Incomprehensible/Flashlight_weapon/Renders&Graphics/21_NAD_flashlight_2_EDIT_1.png

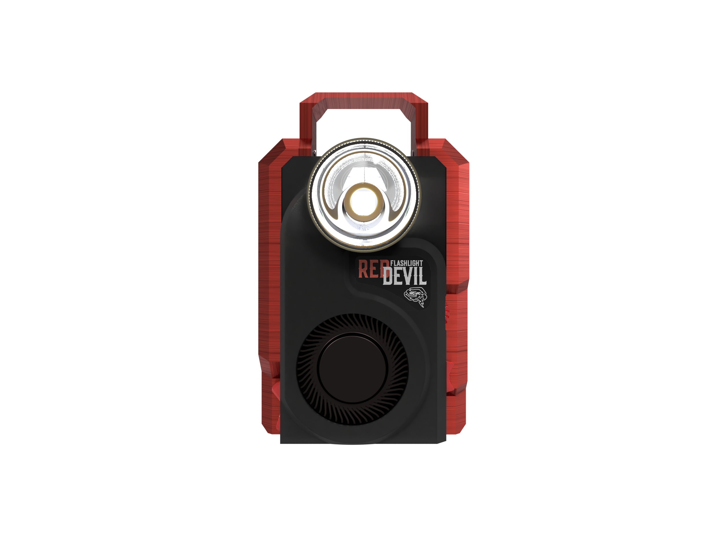
Renders&Graphics/21_NAD_flashlight_2_EDIT_1.png
