Incomprehensible/Flashlight_weapon/Renders&Graphics/21_NAD_flashlight_front_13.png

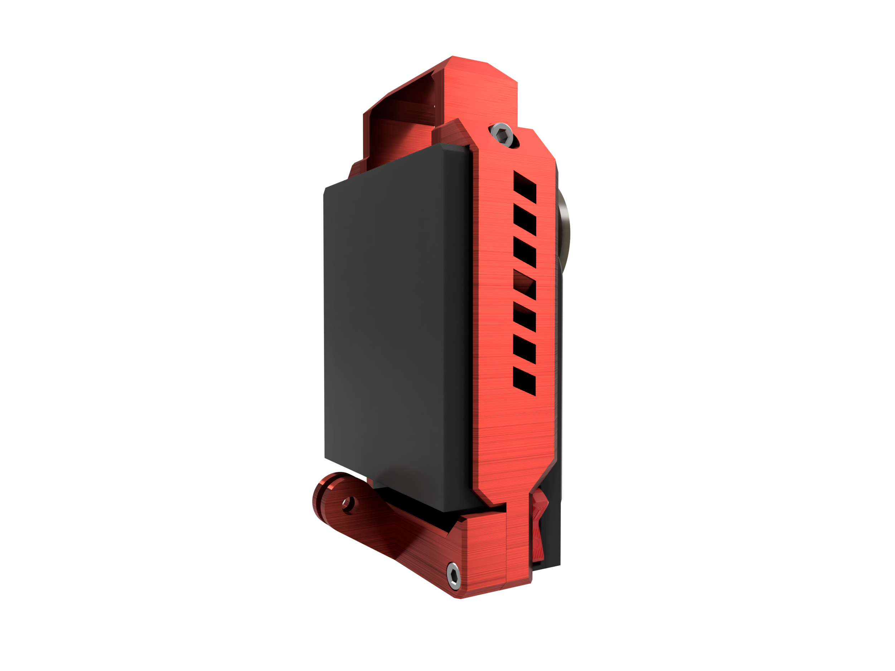
Renders&Graphics/21_NAD_flashlight_front_13.png
