Incomprehensible/Flashlight_weapon/Renders&Graphics/21_NAD_flashlight_front_18.PNG

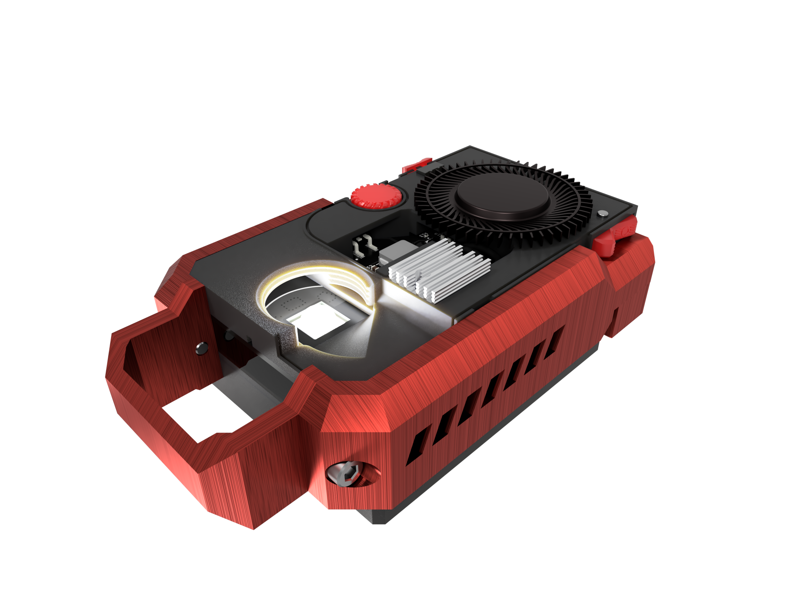
Renders&Graphics/21_NAD_flashlight_front_18.PNG
