Incomprehensible/Flashlight_weapon/KiCad/3D/XT30PW-F.stp

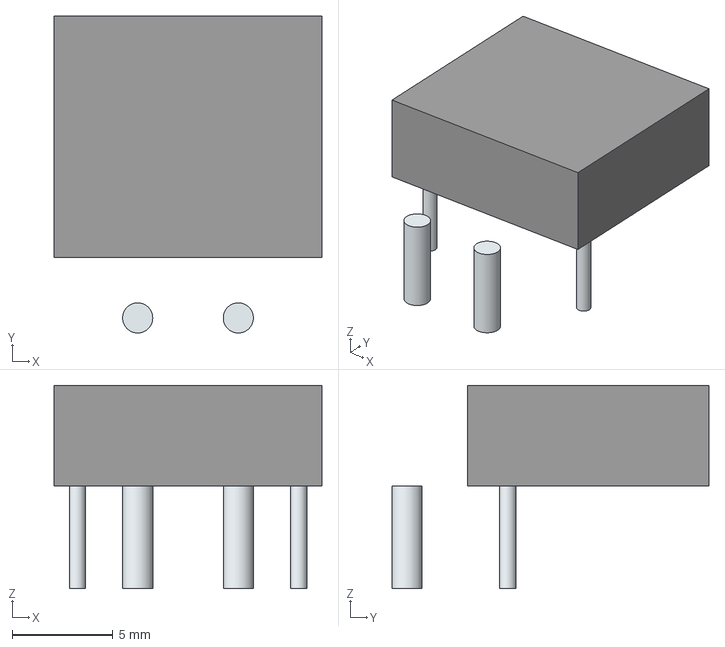
[picture p26: CAD file, 2021-12-03]
KiCad/3D/XT30PW-F.stp
13.3 x 15.7 x 10.1 mm
Leads x 4
