Incomprehensible/Flashlight_weapon/3D_models/Files_for_prototype/Selector_cap_ANY.3mf

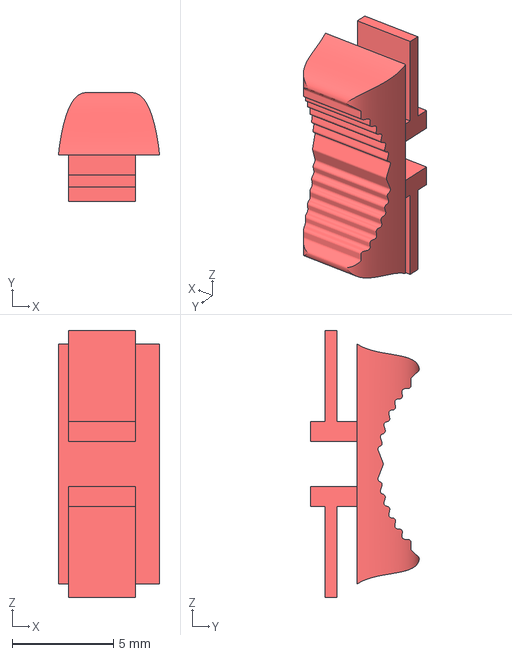
[picture p27: CAD file, 2022-10-16]
3D_models/Files_for_prototype/Selector_cap_ANY.3mf
5.00 x 5.37 x 13.2 mm
