Incomprehensible/Flashlight_weapon/KiCad/3D/IHLP4040DZER2R2M01.stp

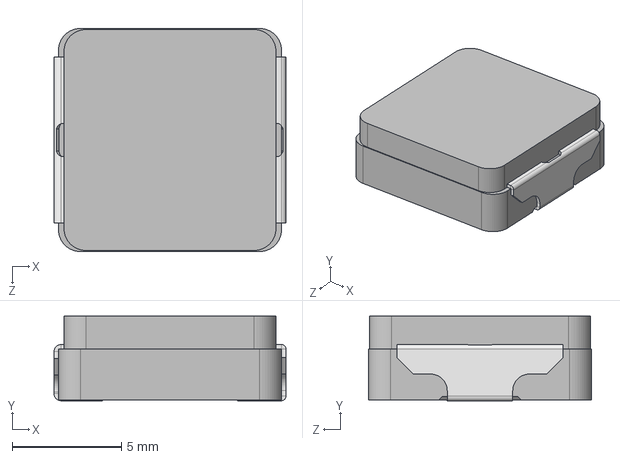
[picture p28: CAD file, 2021-12-03]
KiCad/3D/IHLP4040DZER2R2M01.stp
10.6 x 3.87 x 10.2 mm
