Incomprehensible/Flashlight_weapon/KiCad/3D/VZ067TL1B502.stp

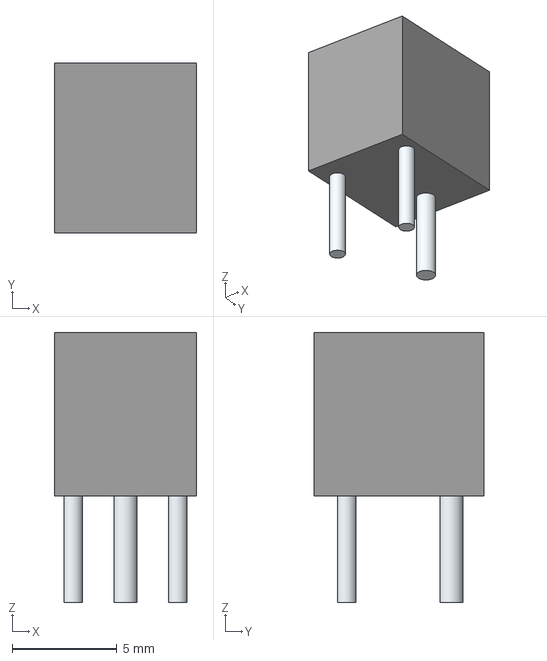
[picture p29: CAD file, 2021-12-03]
KiCad/3D/VZ067TL1B502.stp
6.80 x 8.10 x 12.9 mm
Leads x 3
