Incomprehensible/Flashlight_weapon/3D_models/Files_for_production/2LVL_battery_NYLON_PA12.step

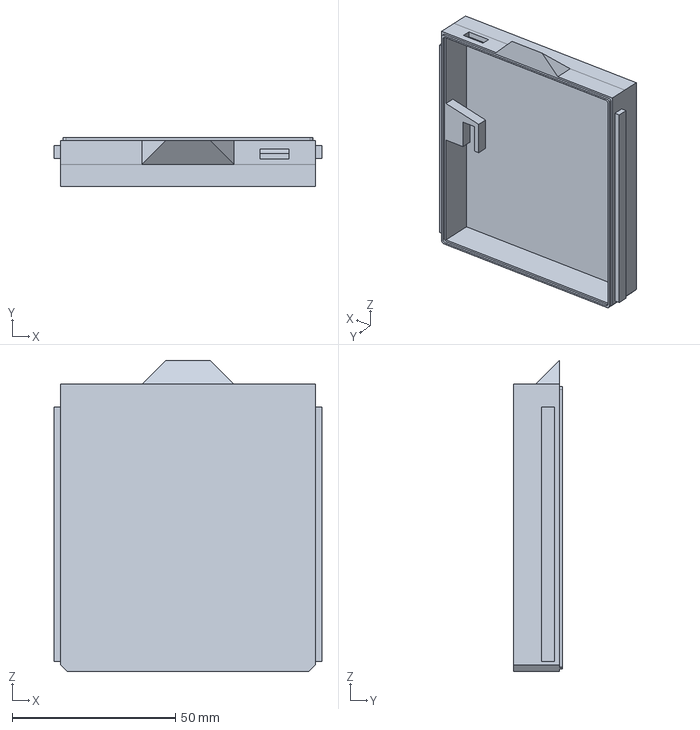
[picture p30: CAD file, 2022-10-16]
3D_models/Files_for_production/2LVL_battery_NYLON_PA12.step
82.0 x 14.9 x 95.2 mm
