Incomprehensible/Flashlight_weapon/KiCad/3D/10TPE47MAZB.step

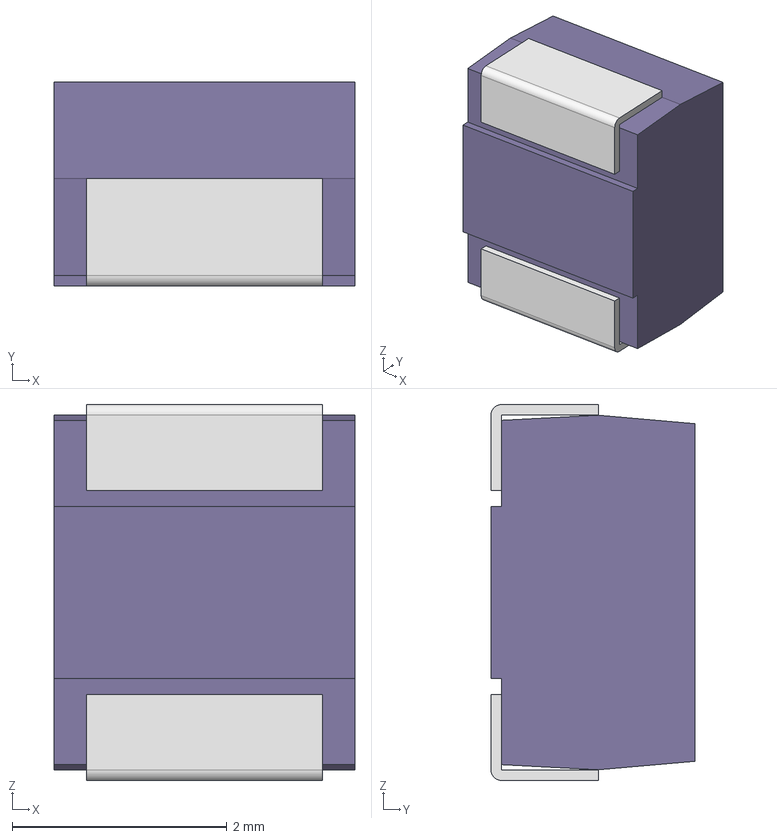
[picture p31: CAD file, 2021-12-03]
KiCad/3D/10TPE47MAZB.step
2.80 x 1.90 x 3.50 mm
mold-B2
flame-B2 x 2
