Incomprehensible/Flashlight_weapon/KiCad/3D/PIC16F716-I_SO.step

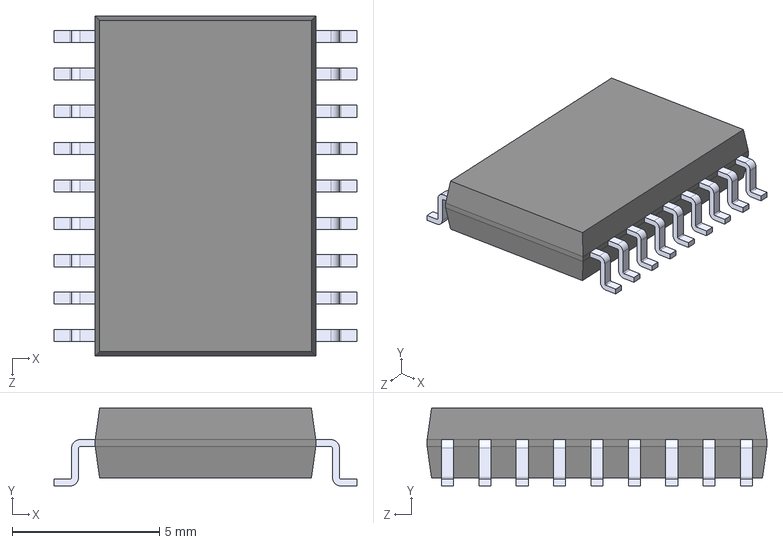
[picture p32: CAD file, 2021-11-05]
KiCad/3D/PIC16F716-I_SO.step
10.3 x 2.65 x 11.6 mm
