Incomprehensible/Flashlight_weapon/3D_models/Files_for_production/Knob_ANY.step

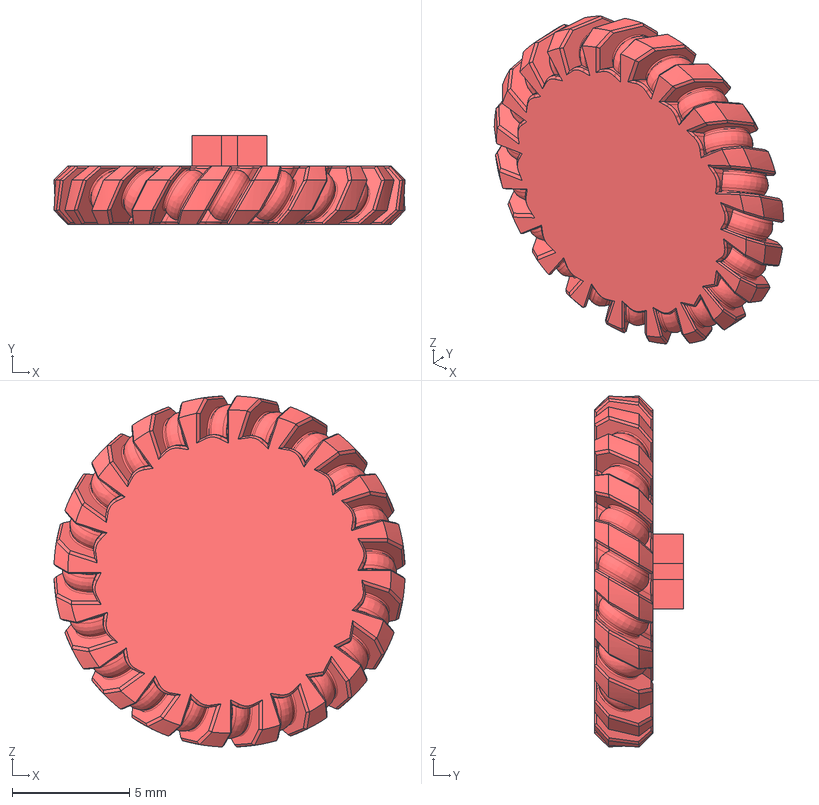
[picture p33: CAD file, 2022-10-16]
3D_models/Files_for_production/Knob_ANY.step
15.0 x 3.80 x 15.0 mm
