Incomprehensible/Flashlight_weapon/3D_models/Files_for_production/BigLens_body_Aluminum.step

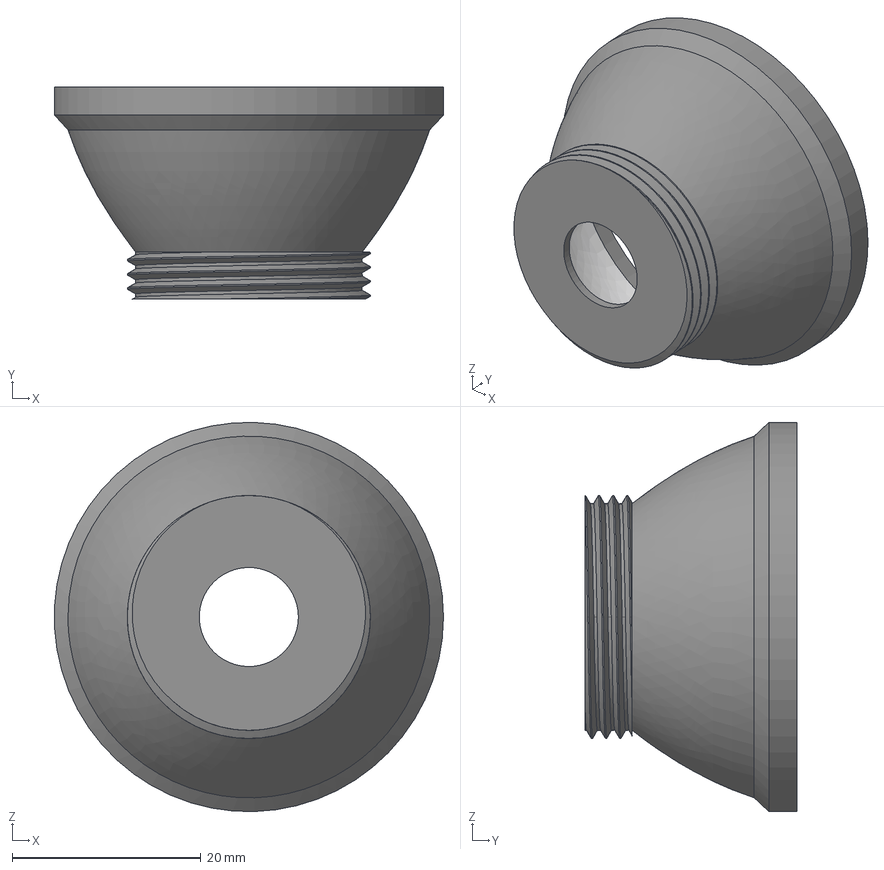
[picture p34: CAD file, 2022-10-16]
3D_models/Files_for_production/BigLens_body_Aluminum.step
41.2 x 22.5 x 41.2 mm
