Incomprehensible/Flashlight_weapon/3D_models/Files_for_prototype/1LVL_base_PETG.3mf

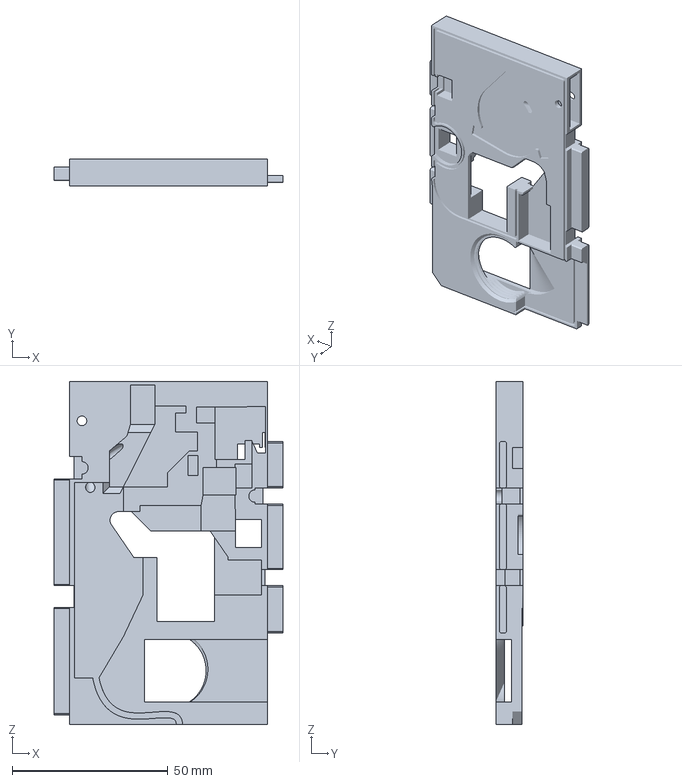
[picture p35: CAD file, 2022-10-16]
3D_models/Files_for_prototype/1LVL_base_PETG.3mf
73.3 x 8.80 x 110.0 mm
